ChrisBall/003_Synth/code/003_synth_main/waveshapeTable.h

#ifndef waveshapeTable_h
#define waveshapeTable_h
#include "Arduino.h"
#include <Audio.h>

#define WAVESHAPE_SIZE 17
const float waveShapes[128][WAVESHAPE_SIZE] = {
  { -1, -0.875, -0.75,  -0.625, -0.5, -0.375, -0.25,  -0.125, -0, 0.125,  0.25, 0.375,  0.5,  0.625,  0.75, 0.875,  1},
  { -1,  -0.876, -0.752, -0.627, -0.503, -0.378, -0.253, -0.127, -0, 0.127,  0.253,  0.378,  0.503,  0.627,  0.752,  0.876,  1},
  { -1,  -0.877, -0.753, -0.63,  -0.505, -0.381, -0.256, -0.129, -0, 0.129,  0.256,  0.381,  0.505,  0.63, 0.753,  0.877,  1},
  { -1,  -0.878, -0.755, -0.632, -0.508, -0.384, -0.258, -0.131, -0, 0.131,  0.258,  0.384,  0.508,  0.632,  0.755,  0.878,  1},
  { -1,  -0.879, -0.757, -0.634, -0.511, -0.387, -0.261, -0.133, -0, 0.133,  0.261,  0.387,  0.511,  0.634,  0.757,  0.879,  1},
  { -1,  -0.88,  -0.759, -0.637, -0.514, -0.39,  -0.264, -0.136, -0, 0.136,  0.264,  0.39, 0.514,  0.637,  0.759,  0.88, 1},
  { -1,  -0.881, -0.76,  -0.639, -0.517, -0.393, -0.267, -0.138, -0, 0.138,  0.267,  0.393,  0.517,  0.639,  0.76, 0.881,  1},
  { -1,  -0.881, -0.762, -0.641, -0.519, -0.396, -0.27,  -0.14,  -0, 0.14, 0.27, 0.396,  0.519,  0.641,  0.762,  0.881,  1},
  { -1,  -0.882, -0.764, -0.644, -0.522, -0.399, -0.273, -0.142, -0, 0.142,  0.273,  0.399,  0.522,  0.644,  0.764,  0.882,  1},
  { -1,  -0.883, -0.765, -0.646, -0.525, -0.402, -0.276, -0.145, -0, 0.145,  0.276,  0.402,  0.525,  0.646,  0.765,  0.883,  1},
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
  { -1,  -0.911, -0.817, -0.719, -0.615, -0.503, -0.379, -0.233, -0, 0.233,  0.379,  0.503,  0.615,  0.719,  0.817,  0.911,  1},
  { -1,  -0.912, -0.819, -0.722, -0.619, -0.507, -0.383, -0.237, -0, 0.237,  0.383,  0.507,  0.619,  0.722,  0.819,  0.912,  1},
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
};

#endif
