ChrisBall/003_Synth/code/modified audio lib files/effect_delay.h

/* Audio Library for Teensy 3.X
 * Copyright (c) 2014, Paul Stoffregen, paul@pjrc.com
 *
 * Development of this audio library was funded by PJRC.COM, LLC by sales of
 * Teensy and Audio Adaptor boards.  Please support PJRC's efforts to develop
 * open source software by purchasing Teensy or other PJRC products.
 *
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
 * THE SOFTWARE IS PROVIDED "AS IS", WITHOUT WARRANTY OF ANY KIND, EXPRESS OR
 * IMPLIED, INCLUDING BUT NOT LIMITED TO THE WARRANTIES OF MERCHANTABILITY,
 * FITNESS FOR A PARTICULAR PURPOSE AND NONINFRINGEMENT. IN NO EVENT SHALL THE
 * AUTHORS OR COPYRIGHT HOLDERS BE LIABLE FOR ANY CLAIM, DAMAGES OR OTHER
 * LIABILITY, WHETHER IN AN ACTION OF CONTRACT, TORT OR OTHERWISE, ARISING FROM,
 * OUT OF OR IN CONNECTION WITH THE SOFTWARE OR THE USE OR OTHER DEALINGS IN
 * THE SOFTWARE.
 */

#ifndef effect_delay_h_
#define effect_delay_h_
#include "Arduino.h"
#include "AudioStream.h"
#include "utility/dspinst.h"

#if defined(__IMXRT1062__)
  // 4.00 second maximum on Teensy 4.0
  #define DELAY_QUEUE_SIZE  (44100 / AUDIO_BLOCK_SAMPLES)  //176400 is default
#elif defined(__MK66FX1M0__)
  // 2.41 second maximum on Teensy 3.6
  #define DELAY_QUEUE_SIZE  (106496 / AUDIO_BLOCK_SAMPLES)
#elif defined(__MK64FX512__)
  // 1.67 second maximum on Teensy 3.5
  #define DELAY_QUEUE_SIZE  (73728 / AUDIO_BLOCK_SAMPLES)
#elif defined(__MK20DX256__)
  // 0.45 second maximum on Teensy 3.1 & 3.2
  #define DELAY_QUEUE_SIZE  (19826 / AUDIO_BLOCK_SAMPLES)
#else
  // 0.14 second maximum on Teensy 3.0
  #define DELAY_QUEUE_SIZE  (6144 / AUDIO_BLOCK_SAMPLES)
#endif

class AudioEffectDelay : public AudioStream
{
public:
	AudioEffectDelay() : AudioStream(1, inputQueueArray) {
		activemask = 0;
		headindex = 0;
		tailindex = 0;
		maxblocks = 0;
		memset(queue, 0, sizeof(queue));
	}
	void delay(uint8_t channel, float milliseconds) {
		if (channel >= 8) return;
		if (milliseconds < 0.0) milliseconds = 0.0;
		uint32_t n = (milliseconds*(AUDIO_SAMPLE_RATE_EXACT/1000.0))+0.5;
		uint32_t nmax = AUDIO_BLOCK_SAMPLES * (DELAY_QUEUE_SIZE-1);
		if (n > nmax) n = nmax;
		uint32_t blks = (n + (AUDIO_BLOCK_SAMPLES-1)) / AUDIO_BLOCK_SAMPLES + 1;
		if (!(activemask & (1<<channel))) {
			// enabling a previously disabled channel
			position[channel] = n;
			if (blks > maxblocks) maxblocks = blks;
			activemask |= (1<<channel);
		} else {
			if (n > position[channel]) {
				// new delay is greater than previous setting
				if (blks > maxblocks) maxblocks = blks;
				position[channel] = n;
			} else {
				// new delay is less than previous setting
				position[channel] = n;
				recompute_maxblocks();
			}
		}
	}
	void disable(uint8_t channel) {
		if (channel >= 8) return;
		// diable this channel
		activemask &= ~(1<<channel);
		// recompute maxblocks for remaining enabled channels
		recompute_maxblocks();
	}
	virtual void update(void);
private:
	void recompute_maxblocks(void) {
		uint32_t max=0;
		uint32_t channel = 0;
		do {
			if (activemask & (1<<channel)) {
				uint32_t n = position[channel];
				n = (n + (AUDIO_BLOCK_SAMPLES-1)) / AUDIO_BLOCK_SAMPLES + 1;
				if (n > max) max = n;
			}
		} while(++channel < 8);
		maxblocks = max;
	}
	uint8_t activemask;   // which output channels are active
	uint16_t headindex;    // head index (incoming) data in quueu
	uint16_t tailindex;    // tail index (outgoing) data from queue
	uint16_t maxblocks;    // number of blocks needed in queue
#if DELAY_QUEUE_SIZE * AUDIO_BLOCK_SAMPLES < 65535
	uint16_t position[8]; // # of sample delay for each channel
#else
	uint32_t position[8]; // # of sample delay for each channel
#endif
	audio_block_t *queue[DELAY_QUEUE_SIZE];
	audio_block_t *inputQueueArray[1];
};

class AudioEffectTapeDelay : public AudioStream {
  public:
  	AudioEffectTapeDelay(void) : AudioStream(1,inputQueueArray){
  		headIndex=0;
  		tailIndex=0;
  		speed=1024;				//1024=normal speed, 512=half speed, etc.
		//memset(queue, 0, sizeof(queue));
  	}
    void setSpeed(float SPEED){  //needs a constraint on speed!
    	speed=uint32_t(SPEED*1024);
    }
    virtual void update(void);
  private:
  	uint16_t getQueueInterp(uint32_t POSITION){  
  		//read the given interpolated position from the queue
  		//we're going to use 10-bit accuracy for calculating interpolation, so maximum DELAY_QUEUE_SIZE will be 4194304 samples (95 seconds)
  		uint32_t LOWER = (POSITION >> 10) % (DELAY_QUEUE_SIZE * AUDIO_BLOCK_SAMPLES);
  		uint32_t UPPER = (LOWER + 1) % (DELAY_QUEUE_SIZE * AUDIO_BLOCK_SAMPLES);
  		uint32_t LOWERBLOCK = LOWER / AUDIO_BLOCK_SAMPLES;
  		uint32_t UPPERBLOCK = UPPER / AUDIO_BLOCK_SAMPLES;
  		uint32_t LOWERSAMP = LOWER % AUDIO_BLOCK_SAMPLES;
  		uint32_t UPPERSAMP = UPPER % AUDIO_BLOCK_SAMPLES;

  		return linInterp1024(queue[LOWERBLOCK].data[LOWERSAMP],
  							queue[UPPERBLOCK].data[UPPERSAMP],
  							POSITION % 1024);
  	}
  	int16_t linInterp1024(int32_t IN1, int32_t IN2, uint16_t WEIGHT){
  		return ((IN1 * (1024 - WEIGHT) + IN2 * WEIGHT) >> 10);
  	}
	uint32_t headIndex;    // head index (incoming) data in queue
	uint32_t tailIndex;    // tail index (outgoing) data from queue
	uint32_t speed;  
  	audio_block_t queue[DELAY_QUEUE_SIZE];
    audio_block_t *inputQueueArray[1];
};

#endif
